TudorAndreiCalciu/InkTime-v6/Images/1.png

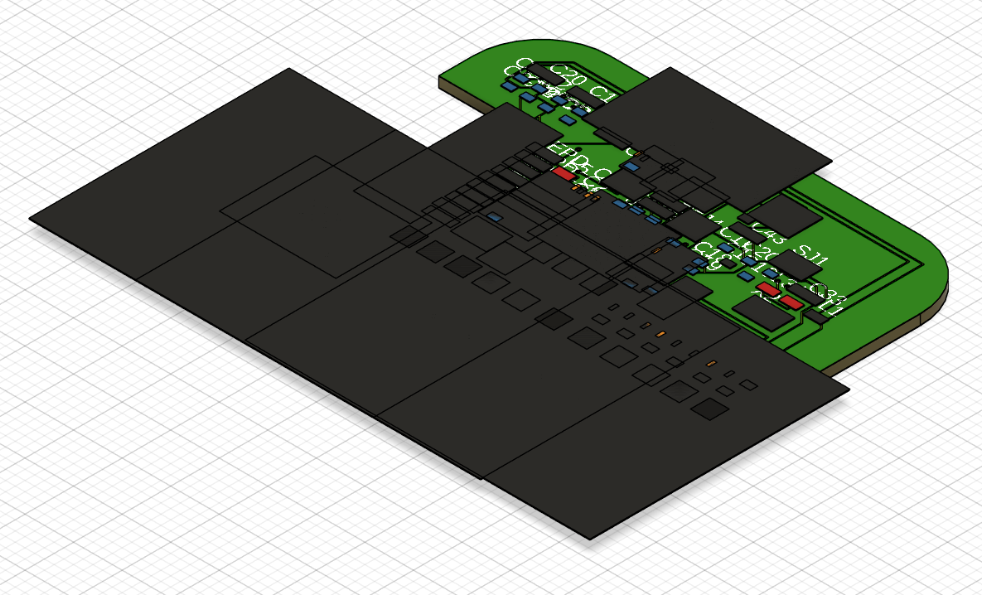
Images/1.png
