TudorAndreiCalciu/InkTime-v6/Images/2.png

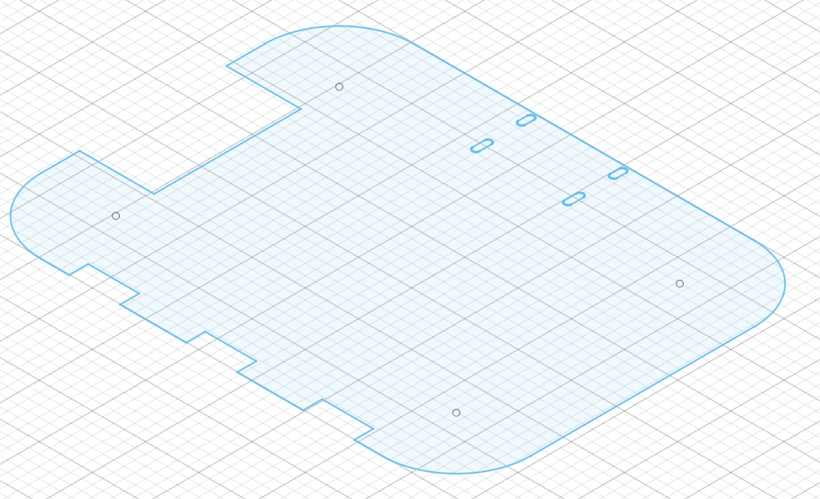
Images/2.png
