TudorAndreiCalciu/InkTime-v6/Images/3.png

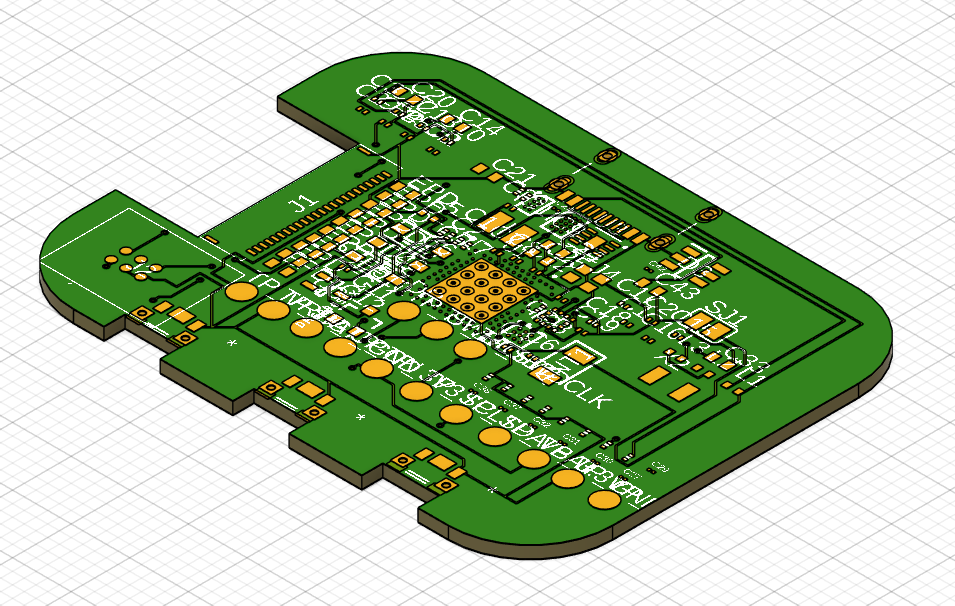
Images/3.png
